notVadoth/NuclearChallenge-StabilityControl/Schematic/dye-rig.kicad_sch

## KiCad design Schematic/dye-rig.kicad_sch (2026-10-06)

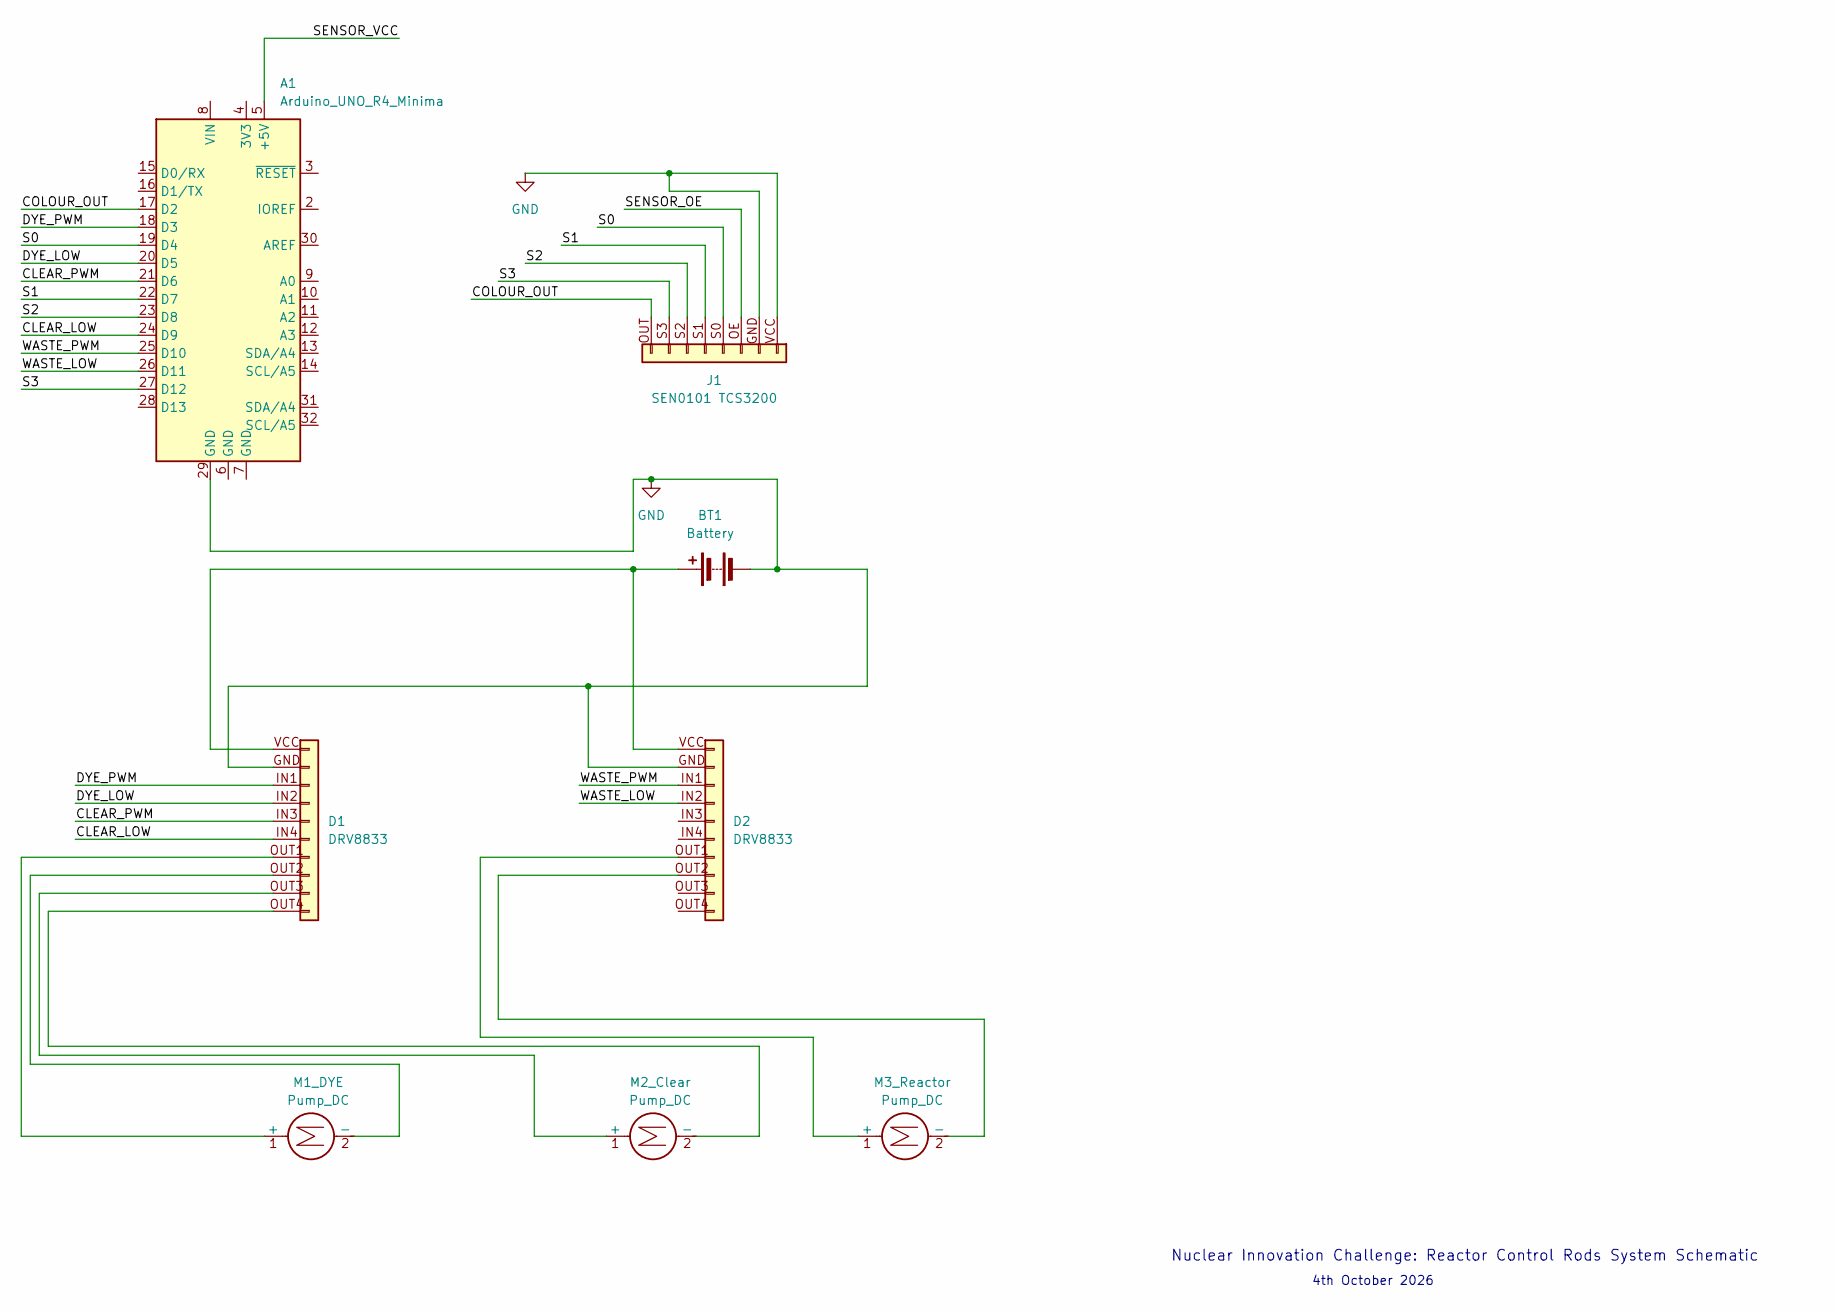
[picture p10: schematic dye-rig.kicad_sch]

Parts:
A1: Arduino_UNO_R4_Minima; Arduino_UNO_R3
BT1: Battery; Texas_DRC0010J_ThermalVias
D1, D2: DRV8833
J1: SEN0101 TCS3200
M1_DYE: Pump_DC; Maple_Mini
M2_Clear, M3_Reactor: Pump_DC

Connections:
CLEAR_LOW: A1.24 (D9), D1.IN4 (Pin_6)
CLEAR_PWM: A1.21 (D6), D1.IN3 (Pin_5)
COLOUR_OUT: A1.17 (D2), J1.OUT (Pin_8)
DYE_LOW: A1.20 (D5), D1.IN2 (Pin_4)
DYE_PWM: A1.18 (D3), D1.IN1 (Pin_3)
GND: A1.29 (GND), BT1.2 (-), D1.GND (Pin_2), D2.GND (Pin_2), J1.GND (Pin_2), J1.VCC (Pin_1)
unnamed: BT1.1 (+), D1.VCC (Pin_1), D2.VCC (Pin_1)
unnamed: D1.OUT1 (Pin_7), M1_DYE.1 (+)
unnamed: D1.OUT2 (Pin_8), M1_DYE.2 (-)
unnamed: D1.OUT3 (Pin_9), M2_Clear.1 (+)
unnamed: D1.OUT4 (Pin_10), M2_Clear.2 (-)
unnamed: D2.OUT1 (Pin_7), M3_Reactor.1 (+)
unnamed: D2.OUT2 (Pin_8), M3_Reactor.2 (-)
S0: A1.19 (D4), J1.S0 (Pin_4)
S1: A1.22 (D7), J1.S1 (Pin_5)
S2: A1.23 (D8), J1.S2 (Pin_6)
S3: A1.27 (D12), J1.S3 (Pin_7)
SENSOR_OE: J1.OE (Pin_3)
SENSOR_VCC: A1.5 (+5V)
WASTE_LOW: A1.26 (D11), D2.IN2 (Pin_4)
WASTE_PWM: A1.25 (D10), D2.IN1 (Pin_3)

Notes on the sheet:
4th October 2026
Nuclear Innovation Challenge: Reactor Control Rods System Schematic
